balenair/balenair/docs/images/matrix-front-rear.png

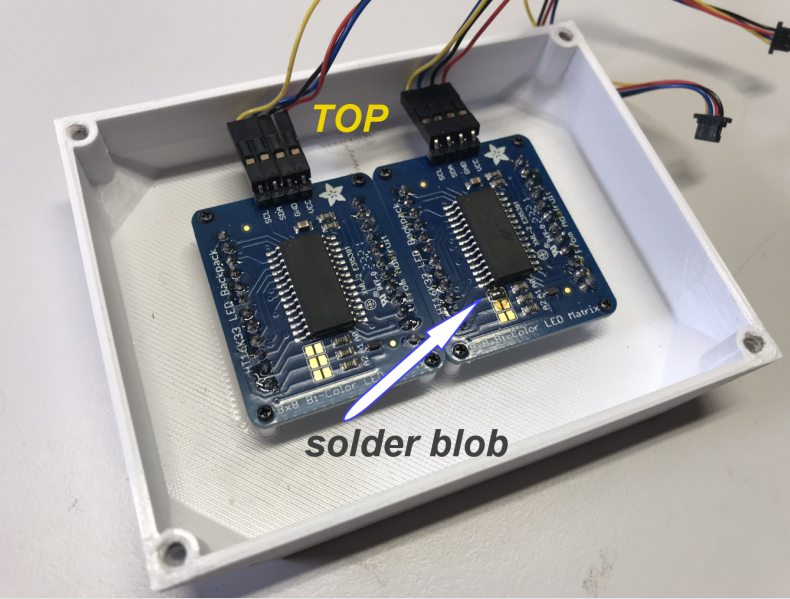
docs/images/matrix-front-rear.png
