balenair/balenair/images/case.png

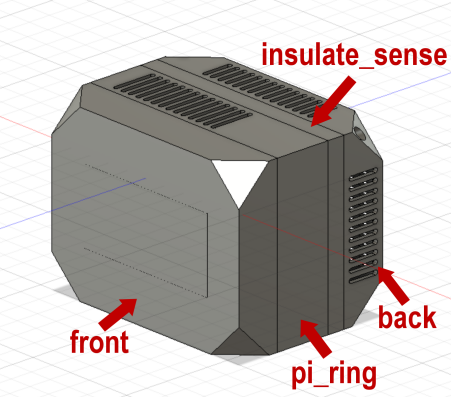
images/case.png
